wuwenfengmi1998/Morse_code_trainer/f103c8t6_keil/MDK-ARM/MYDEIVERS/oled.c

/*
 * oled.c
 *
 *  Created on: 2022年4月15日
 *      Author: wuwen
 */


#include "oled.h"

/*
通过IIC发送指令到OLED
*/
void OLED_WrCmd(unsigned char IIC_Command)
{
	uint8_t *pData;
	pData = &IIC_Command;
	IIC_SAND_DATE(OLED_ADDRESS,0x00,pData,1);
}
/*
通过IIC发送数据到OLED
*/
void OLED_WrDat(unsigned char IIC_Data)
{
	uint8_t *pData;
	pData = &IIC_Data;
	IIC_SAND_DATE(OLED_ADDRESS,0x40,pData,1);
}
/*
设置硬件内的光标
*/
void OLED_Set_Pos(unsigned char x, unsigned char y)
{
  OLED_WrCmd(    0xb0  +   7-y   );
  OLED_WrCmd(((x&0xf0)>>4)|0x10);
  OLED_WrCmd( (x&0x0f)    |0x00);
}
/*
初始化硬件内存（显存）
*/
void OLED_Init_Display_Buffer(char a)
{

	for(unsigned char y = 0;y < Y_WIDTH_;y++)
	{
		OLED_Set_Pos(0,y);
		for(unsigned char x = 0;x < X_WIDTH;x++)
		{

			OLED_WrDat(a);
			//HAL_Delay(1);
		}
	}


}
/*
设置屏幕亮度
*/
void OLED_Setting_luminance(unsigned char a)
{
	OLED_WrCmd(0x81);
	OLED_WrCmd(a*2.55);

}
/*
初始化OLED

硬件扫描方式

从左到右从上到下
纵向8点上高位

*/
void OLED_Init(void)
{
	//HAL_Delay(200);
	OLED_WrCmd(0xAE); //关闭显示
	OLED_WrCmd(0xD5); //设置时钟分频因子,震荡频率
	OLED_WrCmd(  80); //[3:0],分频因子;[7:4],震荡频率
	OLED_WrCmd(0xA8); //设置驱动路数
	OLED_WrCmd(0X3F); //默认0X3F(1/64)
	OLED_WrCmd(0xD3); //设置显示偏移
	OLED_WrCmd(0X00); //默认为0
	OLED_WrCmd(0x40); //设置显示开始行 [5:0],行数.
	OLED_WrCmd(0x8D); //电荷泵设置
	OLED_WrCmd(0x14); //bit2，开启/关闭
	OLED_WrCmd(0x20); //设置内存地址模式
	OLED_WrCmd(0x02); //[1:0],00，列地址模式;01，行地址模式;10,页地址模式;默认10;
	OLED_WrCmd(0xA1); //段重定义设置,bit0:0,0->0;1,0->127;
	OLED_WrCmd(0xC0); //设置COM扫描方向;bit3:0,普通模式;1,重定义模式 COM[N-1]->COM0;N:驱动路数
	//OLED_WrCmd(0xDA); //设置COM硬件引脚配置
	//OLED_WrCmd(0x12); //[5:4]配置
	//显示方向设置
	//OLED_WrCmd(0xc8);//OLED_WrCmd(0xa0);
	 //行扫描顺序：从上到下
	 //列扫描顺序：从左到右
	OLED_WrCmd(0xD9); //设置预充电周期
	OLED_WrCmd(0xf1); //[3:0],PHASE 1;[7:4],PHASE 2;
	OLED_WrCmd(0xDB); //设置VCOMH 电压倍率
	OLED_WrCmd(0x30); //[6:4] 000,0.65*vcc;001,0.77*vcc;011,0.83*vcc;

	OLED_WrCmd(0xA4); //全局显示开启;bit0:1,开启;0,关闭;(白屏/黑屏)
	OLED_WrCmd(0xA6);
	 //设置显示方式;bit0:1,反相显示;0,正常显示
	OLED_WrCmd(0xAF); //开启显示
	
	OLED_Init_Display_Buffer(0);
}

/*************************************************************************************************************************************************************************************/
/*硬件与软件之间的部分*/


/*
定义显存
*/
char OLED_buff[Y_WIDTH_][X_WIDTH];

/*
加速缓存
*/
char OLED_speedup[Y_WIDTH_][X_WIDTH];
/*
将显存发送到硬件
*/
void OLED_Cache_to_hardware()
{
	char b=0;
	for(uint8_t y=0;y<Y_WIDTH_;y++)
	{
		OLED_Set_Pos(0,y);
		for(uint8_t x=0;x<X_WIDTH;x++)
		{
			if(OLED_buff[y][x]!=OLED_speedup[y][x])
			{
				
				if(b==0){b=1;OLED_Set_Pos(x,y);}			
				OLED_WrDat(OLED_buff[y][x]);			
				OLED_speedup[y][x]=OLED_buff[y][x];
				
			}else
			{b=0;}
			OLED_buff[y][x]=0x00;
		}
	}
}


/*************************************************************************************************************************************************************************************/
//5*8 ASCII字符集点阵
const char asc2_0805[95][8]={
/*-- ID:0,字符:" ",ASCII编码:20,对应字:宽x高=5x8,画布:宽W=8 高H=8,共8字节*/
0x00,0x00,0x00,0x00,0x00,0x00,0x00,0x00,
/*-- ID:1,字符:"!",ASCII编码:21,对应字:宽x高=5x8,画布:宽W=8 高H=8,共8字节*/
0x20,0x20,0x20,0x20,0x20,0x00,0x20,0x00,
/*-- ID:2,字符:""",ASCII编码:22,对应字:宽x高=5x8,画布:宽W=8 高H=8,共8字节*/
0x50,0x50,0x50,0x00,0x00,0x00,0x00,0x00,
/*-- ID:3,字符:"#",ASCII编码:23,对应字:宽x高=5x8,画布:宽W=8 高H=8,共8字节*/
0x50,0x50,0xF8,0x50,0xF8,0x50,0x50,0x00,
/*-- ID:4,字符:"$",ASCII编码:24,对应字:宽x高=5x8,画布:宽W=8 高H=8,共8字节*/
0x20,0x78,0xC0,0x70,0x28,0xF0,0x20,0x00,
/*-- ID:5,字符:"%",ASCII编码:25,对应字:宽x高=5x8,画布:宽W=8 高H=8,共8字节*/
0xC0,0xC8,0x10,0x20,0x40,0x98,0x18,0x00,
/*-- ID:6,字符:"&",ASCII编码:26,对应字:宽x高=5x8,画布:宽W=8 高H=8,共8字节*/
0x40,0xA0,0xA0,0x40,0xA8,0x90,0x68,0x00,
/*-- ID:7,字符:"'",ASCII编码:27,对应字:宽x高=5x8,画布:宽W=8 高H=8,共8字节*/
0x30,0x20,0x40,0x00,0x00,0x00,0x00,0x00,
/*-- ID:8,字符:"(",ASCII编码:28,对应字:宽x高=5x8,画布:宽W=8 高H=8,共8字节*/
0x10,0x20,0x40,0x40,0x40,0x20,0x10,0x00,
/*-- ID:9,字符:")",ASCII编码:29,对应字:宽x高=5x8,画布:宽W=8 高H=8,共8字节*/
0x40,0x20,0x10,0x10,0x10,0x20,0x40,0x00,
/*-- ID:10,字符:"*",ASCII编码:2A,对应字:宽x高=5x8,画布:宽W=8 高H=8,共8字节*/
0x20,0xA8,0x70,0x20,0x70,0xA8,0x20,0x00,
/*-- ID:11,字符:"+",ASCII编码:2B,对应字:宽x高=5x8,画布:宽W=8 高H=8,共8字节*/
0x20,0x20,0x20,0xF8,0x20,0x20,0x20,0x00,
/*-- ID:12,字符:",",ASCII编码:2C,对应字:宽x高=5x8,画布:宽W=8 高H=8,共8字节*/
0x00,0x00,0x00,0x00,0x60,0x40,0x80,0x00,
/*-- ID:13,字符:"-",ASCII编码:2D,对应字:宽x高=5x8,画布:宽W=8 高H=8,共8字节*/
0x00,0x00,0x00,0xF8,0x00,0x00,0x00,0x00,
/*-- ID:14,字符:".",ASCII编码:2E,对应字:宽x高=5x8,画布:宽W=8 高H=8,共8字节*/
0x00,0x00,0x00,0x00,0x00,0x60,0x60,0x00,
/*-- ID:15,字符:"/",ASCII编码:2F,对应字:宽x高=5x8,画布:宽W=8 高H=8,共8字节*/
0x00,0x08,0x10,0x20,0x40,0x80,0x00,0x00,
/*-- ID:16,字符:"0",ASCII编码:30,对应字:宽x高=5x8,画布:宽W=8 高H=8,共8字节*/
0x70,0x88,0x98,0xA8,0xC8,0x88,0x70,0x00,
/*-- ID:17,字符:"1",ASCII编码:31,对应字:宽x高=5x8,画布:宽W=8 高H=8,共8字节*/
0x20,0x60,0x20,0x20,0x20,0x20,0x70,0x00,
/*-- ID:18,字符:"2",ASCII编码:32,对应字:宽x高=5x8,画布:宽W=8 高H=8,共8字节*/
0x70,0x88,0x08,0x30,0x40,0x80,0xF8,0x00,
/*-- ID:19,字符:"3",ASCII编码:33,对应字:宽x高=5x8,画布:宽W=8 高H=8,共8字节*/
0xF8,0x08,0x10,0x30,0x08,0x88,0x70,0x00,
/*-- ID:20,字符:"4",ASCII编码:34,对应字:宽x高=5x8,画布:宽W=8 高H=8,共8字节*/
0x10,0x30,0x50,0x90,0xF8,0x10,0x10,0x00,
/*-- ID:21,字符:"5",ASCII编码:35,对应字:宽x高=5x8,画布:宽W=8 高H=8,共8字节*/
0xF8,0x80,0xF0,0x08,0x08,0x88,0x70,0x00,
/*-- ID:22,字符:"6",ASCII编码:36,对应字:宽x高=5x8,画布:宽W=8 高H=8,共8字节*/
0x38,0x40,0x80,0xF0,0x88,0x88,0x70,0x00,
/*-- ID:23,字符:"7",ASCII编码:37,对应字:宽x高=5x8,画布:宽W=8 高H=8,共8字节*/
0xF8,0x08,0x10,0x20,0x40,0x40,0x40,0x00,
/*-- ID:24,字符:"8",ASCII编码:38,对应字:宽x高=5x8,画布:宽W=8 高H=8,共8字节*/
0x70,0x88,0x88,0x70,0x88,0x88,0x70,0x00,
/*-- ID:25,字符:"9",ASCII编码:39,对应字:宽x高=5x8,画布:宽W=8 高H=8,共8字节*/
0x70,0x88,0x88,0x78,0x08,0x10,0xE0,0x00,
/*-- ID:26,字符:":",ASCII编码:3A,对应字:宽x高=5x8,画布:宽W=8 高H=8,共8字节*/
0x00,0x60,0x60,0x00,0x60,0x60,0x00,0x00,
/*-- ID:27,字符:";",ASCII编码:3B,对应字:宽x高=5x8,画布:宽W=8 高H=8,共8字节*/
0x00,0x60,0x60,0x00,0x60,0x60,0x80,0x00,
/*-- ID:28,字符:"<",ASCII编码:3C,对应字:宽x高=5x8,画布:宽W=8 高H=8,共8字节*/
0x10,0x20,0x40,0x80,0x40,0x20,0x10,0x00,
/*-- ID:29,字符:"=",ASCII编码:3D,对应字:宽x高=5x8,画布:宽W=8 高H=8,共8字节*/
0x00,0x00,0xF8,0x00,0xF8,0x00,0x00,0x00,
/*-- ID:30,字符:">",ASCII编码:3E,对应字:宽x高=5x8,画布:宽W=8 高H=8,共8字节*/
0x40,0x20,0x10,0x08,0x10,0x20,0x40,0x00,
/*-- ID:31,字符:"?",ASCII编码:3F,对应字:宽x高=5x8,画布:宽W=8 高H=8,共8字节*/
0x70,0x88,0x10,0x20,0x20,0x00,0x20,0x00,
/*-- ID:32,字符:"@",ASCII编码:40,对应字:宽x高=5x8,画布:宽W=8 高H=8,共8字节*/
0x70,0x88,0xB8,0xA8,0xB8,0x80,0x78,0x00,
/*-- ID:33,字符:"A",ASCII编码:41,对应字:宽x高=5x8,画布:宽W=8 高H=8,共8字节*/
0x20,0x50,0x88,0x88,0xF8,0x88,0x88,0x00,
/*-- ID:34,字符:"B",ASCII编码:42,对应字:宽x高=5x8,画布:宽W=8 高H=8,共8字节*/
0xF0,0x88,0x88,0xF0,0x88,0x88,0xF0,0x00,
/*-- ID:35,字符:"C",ASCII编码:43,对应字:宽x高=5x8,画布:宽W=8 高H=8,共8字节*/
0x70,0x88,0x80,0x80,0x80,0x88,0x70,0x00,
/*-- ID:36,字符:"D",ASCII编码:44,对应字:宽x高=5x8,画布:宽W=8 高H=8,共8字节*/
0xF0,0x88,0x88,0x88,0x88,0x88,0xF0,0x00,
/*-- ID:37,字符:"E",ASCII编码:45,对应字:宽x高=5x8,画布:宽W=8 高H=8,共8字节*/
0xF8,0x80,0x80,0xF0,0x80,0x80,0xF8,0x00,
/*-- ID:38,字符:"F",ASCII编码:46,对应字:宽x高=5x8,画布:宽W=8 高H=8,共8字节*/
0xF8,0x80,0x80,0xF0,0x80,0x80,0x80,0x00,
/*-- ID:39,字符:"G",ASCII编码:47,对应字:宽x高=5x8,画布:宽W=8 高H=8,共8字节*/
0x70,0x88,0x80,0x80,0xB8,0x88,0x78,0x00,
/*-- ID:40,字符:"H",ASCII编码:48,对应字:宽x高=5x8,画布:宽W=8 高H=8,共8字节*/
0x88,0x88,0x88,0xF8,0x88,0x88,0x88,0x00,
/*-- ID:41,字符:"I",ASCII编码:49,对应字:宽x高=5x8,画布:宽W=8 高H=8,共8字节*/
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

/*-- ID:91,字符:"{",ASCII编码:7B,对应字:宽x高=8x16,画布:宽W=8 高H=16,共16字节*/
0x00,0x00,0x00,0x0E,0x18,0x18,0x18,0x70,0x18,0x18,0x18,0x18,0x0E,0x00,0x00,0x00,

/*-- ID:92,字符:"|",ASCII编码:7C,对应字:宽x高=8x16,画布:宽W=8 高H=16,共16字节*/
0x00,0x00,0x00,0x18,0x18,0x18,0x18,0x00,0x18,0x18,0x18,0x18,0x18,0x00,0x00,0x00,

/*-- ID:93,字符:"}",ASCII编码:7D,对应字:宽x高=8x16,画布:宽W=8 高H=16,共16字节*/
0x00,0x00,0x00,0x70,0x18,0x18,0x18,0x0E,0x18,0x18,0x18,0x18,0x70,0x00,0x00,0x00,

/*-- ID:94,字符:"~",ASCII编码:7E,对应字:宽x高=8x16,画布:宽W=8 高H=16,共16字节*/
0x00,0x00,0x00,0x76,0xDC,0x00,0x00,0x00,0x00,0x00,0x00,0x00,0x00,0x00,0x00,0x00

};

/*
打点函数
打点类型
dot_type=0 清除点
				=1 打点
				=2 取反点
*/
void OLED_set_dot(unsigned char x,unsigned char y,unsigned char dot_type)
{
	if(x>=X_WIDTH||y>=Y_WIDTH)
	{
		return ;
	}
	uint8_t y1=y/8;
	uint8_t y2=y%8;
	uint8_t y3=(0x80>>y2);
	
	char temp=OLED_buff[y1][x];
	switch(dot_type)
	{
		case 0:
			temp &= ~y3;
			break;
		case 1:
			temp |= y3;
			break;
		case 2:
			temp ^= y3;
			break;
		case 3:break;
	}
	
	
	OLED_buff[y1][x]=temp;
		
		
	
	
}
/*
绘图函数
数据格式 从左到右，从上到下，横向8点右高位
type=0 清空区域
		=1 区域图层
		=2 正片叠底
		=3 正片清空
		=4 负片
		=5 正片负片
*/
void OLED_Pix(unsigned char x,unsigned char y,unsigned char w,unsigned char h,const char *p,unsigned char type)
{
	
	unsigned char b=0;
	unsigned int  c=0;
	
	for(uint8_t h1=0;h1<h;h1++)
	{
		for(uint8_t w1=0;w1<w;w1++)
		{
			if(p[c]&0x80>>b)
			{
				switch(type)
				{
					case 0:
						OLED_set_dot(w1+x,h1+y,0);
						break;
					case 1:
						OLED_set_dot(w1+x,h1+y,1);
						break;
					case 2:
						OLED_set_dot(w1+x,h1+y,1);
						break;		
					case 3:
						OLED_set_dot(w1+x,h1+y,0);
						break;		
					case 4:
						OLED_set_dot(w1+x,h1+y,0);
						break;	
					case 5:
						OLED_set_dot(w1+x,h1+y,2);
						break;						
				}
				
			}else
			{
				switch(type)
				{
					case 0:
						OLED_set_dot(w1+x,h1+y,0);
						break;
					case 1:
						OLED_set_dot(w1+x,h1+y,0);
						break;
					case 2:

						break;	
					case 4:
						OLED_set_dot(w1+x,h1+y,1);
						break;
				}
			}
			b++;
			if(b==8)
			{
				b=0;c++;
			}
		}
		if(b!=0)
		{
			b=0;c++;
		}
		
	}
		
	

}
/*
显示字符
数据格式 从左到右，从上到下，横向8点左高位 （同一个函数实现的显示不知道为何这里要用左高位才能正常显示）
type=0 清空区域
		=1 区域图层
		=2 正片叠底
		=3 正片清空
		=4 负片
*/
void OLED_Ascii(unsigned char x,unsigned char y,unsigned char size,char chr,unsigned char type)
{
	if(chr>=' '&&chr<='~')
	{
		switch(size)
		{
			case 8:
				OLED_Pix(x,y,5,8,asc2_0805[chr-' '],type);
				break;			
			case 12:
				OLED_Pix(x,y,6,12,asc2_1206[chr-' '],type);
				break;
			case 16:
				OLED_Pix(x,y,8,16,asc2_1608[chr-' '],type);
				break;
		}	
	}

}

void OLED_Str(unsigned char x,unsigned char y,unsigned char size,char *str,unsigned char type)
{
	unsigned char size2;
	switch(size)
	{
		case 8:
			size2=6;
		break;
		case 12:
			size2=7;
		break;
		case 16:
			size2=8;
		break;
	}	
	
	while(*str!='\0')
	{
		if(x+size2>=X_WIDTH)
		{
			y+=size;
			if(y>=Y_WIDTH)
			{
				y=0;
			}
			x=0;
		}

		OLED_Ascii(x,y,size,*str,type);

		str++;
		
		x+=size2;
		
		

	}

}

/*
几何绘图
*/


/*画横线*/
void OLED_HL(unsigned char x,unsigned char y,unsigned char size,unsigned char dot_type)
{

}

/*画竖线*/
void OLED_VL(unsigned char x,unsigned char y,unsigned char size,unsigned char dot_type)
{

}

/*画任意线*/
void OLED_AL(int sx,int sy,int ex,int ey,unsigned char dot_type)
{

	int dx,dy,absx,absy;
	
	//计算差
	dx=ex-sx;
	dy=ey-sy;
	//取绝对值 就是轴长
	absx=dx<0?0-dx:dx;
	absy=dy<0?0-dy:dy;
	
	
	if(dx==0)
	{
		if(dy>0)
		{
			for(int y=ey;y>sy;y--)
			{
				OLED_set_dot(sx,y,dot_type);
			}
		}else 
		if(dy<0)
		{
			for(int y=ey;y<sy;y++)
			{
				OLED_set_dot(sx,y,dot_type);
			}
		}
		
		return ;
	}

	if(dy==0)
	{
		if(dx>0)
		{
			for(int x=ex;x>sx;x--)
			{
				OLED_set_dot(x,sy,dot_type);
			}
		}else
		if(dx<0)
		{
			for(int x=ex;x<sx;x++)
			{
				OLED_set_dot(x,sy,dot_type);
			}
		}
		
		return ;
	}
	
	if(dx==0&&dy==0)
	{
		//OLED_set_dot(sx,sy,dot_type);
		return ;
	}
}


/*画方框*/
void OLED_square(int Start_x, int Start_y, int End_x, int End_y, char type)
{
	if(Start_x > End_x){int i1 = Start_x; Start_x = End_x; End_x=i1;}
	if(Start_y > End_y){int i1 = Start_y; Start_y = End_y; End_y=i1;}
	for(; Start_x < End_x ; Start_x++)
	{
		for(int y2 = Start_y ; y2 < End_y ; y2++)
		{
			OLED_set_dot(Start_x, y2, type);
		}
	}
}

int SHOW_MENU(menu *m,int encoder,char button,char lan)
{
	int return_code=-1;
	char str[32];
	const char *list;
	uint16_t list_len=0;
	uint16_t a=0;
	uint16_t b=0;
	uint16_t c=0;
	uint16_t d=0;

	//get list
	switch(lan)
	{
	case 0:
		list=m->list_en;
		break;
	case 1:
		list=m->list_ch;
		break;
	default :
		return -1;

	}



	//check how many list
	while(list[a]!='\0')
	{
		if(list[a]=='\n'){list_len++;}
		a++;
	}

	m->sele+=encoder;

	if(m->sele<0){m->sele=0;}
	if(m->sele>list_len){m->sele=list_len;}

	if(m->sele<m->list_dis_top+3){m->list_dis_top--;}
	if(m->sele>m->list_dis_top){if((m->list_dis_top+3)<list_len){m->list_dis_top++;}}

	m->list_dis_top=((list_len+1>4)?(m->list_dis_top):0);

	//display list
	for(d=0;d<m->list_dis_top;d++)
	{
		while((*list!='\0')&&(*list!='\n'))
		{
			list++;
		}
		list++;

	}


	for(b=0;b<(list_len+1>4?4:list_len+1);b++)
	{
		if((m->list_dis_top+b)==m->sele)
		{
			str[c]='>';

		}else
		{
			str[c]=' ';
		}
		c++;
		while((*list!='\0')&&(*list!='\n'))
		{
			str[c]=*list;
			c++;
			list++;
		}
		str[c]='\0';
		OLED_Str(0, 16*b, 16, str, 1);
		c=0;
		list++;

	}

	if(button==1)
	{
		return_code=m->sele;
	}

	return return_code;

}
