wuwenfengmi1998/Morse_code_trainer/f103c8t6_HAL/MYDRIVERS/oled.c

/*
 * oled.c
 *
 *  Created on: 2022年4月15日
 *      Author: wuwen
 */


#include "oled.h"


//16*16 ASCII字符集点阵
const unsigned char asc2_1608[95][16]={
{0x00,0x00,0x00,0x00,0x00,0x00,0x00,0x00,0x00,0x00,0x00,0x00,0x00,0x00,0x00,0x00},/*" ",0*/
{0x00,0x00,0x00,0x00,0x00,0x00,0x1F,0xCC,0x00,0x0C,0x00,0x00,0x00,0x00,0x00,0x00},/*"!",1*/
{0x00,0x00,0x08,0x00,0x30,0x00,0x60,0x00,0x08,0x00,0x30,0x00,0x60,0x00,0x00,0x00},/*""",2*/
{0x02,0x20,0x03,0xFC,0x1E,0x20,0x02,0x20,0x03,0xFC,0x1E,0x20,0x02,0x20,0x00,0x00},/*"#",3*/
{0x00,0x00,0x0E,0x18,0x11,0x04,0x3F,0xFF,0x10,0x84,0x0C,0x78,0x00,0x00,0x00,0x00},/*"$",4*/
{0x0F,0x00,0x10,0x84,0x0F,0x38,0x00,0xC0,0x07,0x78,0x18,0x84,0x00,0x78,0x00,0x00},/*"%",5*/
{0x00,0x78,0x0F,0x84,0x10,0xC4,0x11,0x24,0x0E,0x98,0x00,0xE4,0x00,0x84,0x00,0x08},/*"&",6*/
{0x08,0x00,0x68,0x00,0x70,0x00,0x00,0x00,0x00,0x00,0x00,0x00,0x00,0x00,0x00,0x00},/*"'",7*/
{0x00,0x00,0x00,0x00,0x00,0x00,0x07,0xE0,0x18,0x18,0x20,0x04,0x40,0x02,0x00,0x00},/*"(",8*/
{0x00,0x00,0x40,0x02,0x20,0x04,0x18,0x18,0x07,0xE0,0x00,0x00,0x00,0x00,0x00,0x00},/*")",9*/
{0x02,0x40,0x02,0x40,0x01,0x80,0x0F,0xF0,0x01,0x80,0x02,0x40,0x02,0x40,0x00,0x00},/*"*",10*/
{0x00,0x80,0x00,0x80,0x00,0x80,0x0F,0xF8,0x00,0x80,0x00,0x80,0x00,0x80,0x00,0x00},/*"+",11*/
{0x00,0x01,0x00,0x0D,0x00,0x0E,0x00,0x00,0x00,0x00,0x00,0x00,0x00,0x00,0x00,0x00},/*",",12*/
{0x00,0x00,0x00,0x80,0x00,0x80,0x00,0x80,0x00,0x80,0x00,0x80,0x00,0x80,0x00,0x80},/*"-",13*/
{0x00,0x00,0x00,0x0C,0x00,0x0C,0x00,0x00,0x00,0x00,0x00,0x00,0x00,0x00,0x00,0x00},/*".",14*/
{0x00,0x00,0x00,0x06,0x00,0x18,0x00,0x60,0x01,0x80,0x06,0x00,0x18,0x00,0x20,0x00},/*"/",15*/
{0x00,0x00,0x07,0xF0,0x08,0x08,0x10,0x04,0x10,0x04,0x08,0x08,0x07,0xF0,0x00,0x00},/*"0",16*/
{0x00,0x00,0x08,0x04,0x08,0x04,0x1F,0xFC,0x00,0x04,0x00,0x04,0x00,0x00,0x00,0x00},/*"1",17*/
{0x00,0x00,0x0E,0x0C,0x10,0x14,0x10,0x24,0x10,0x44,0x11,0x84,0x0E,0x0C,0x00,0x00},/*"2",18*/
{0x00,0x00,0x0C,0x18,0x10,0x04,0x11,0x04,0x11,0x04,0x12,0x88,0x0C,0x70,0x00,0x00},/*"3",19*/
{0x00,0x00,0x00,0xE0,0x03,0x20,0x04,0x24,0x08,0x24,0x1F,0xFC,0x00,0x24,0x00,0x00},/*"4",20*/
{0x00,0x00,0x1F,0x98,0x10,0x84,0x11,0x04,0x11,0x04,0x10,0x88,0x10,0x70,0x00,0x00},/*"5",21*/
{0x00,0x00,0x07,0xF0,0x08,0x88,0x11,0x04,0x11,0x04,0x18,0x88,0x00,0x70,0x00,0x00},/*"6",22*/
{0x00,0x00,0x1C,0x00,0x10,0x00,0x10,0xFC,0x13,0x00,0x1C,0x00,0x10,0x00,0x00,0x00},/*"7",23*/
{0x00,0x00,0x0E,0x38,0x11,0x44,0x10,0x84,0x10,0x84,0x11,0x44,0x0E,0x38,0x00,0x00},/*"8",24*/
{0x00,0x00,0x07,0x00,0x08,0x8C,0x10,0x44,0x10,0x44,0x08,0x88,0x07,0xF0,0x00,0x00},/*"9",25*/
{0x00,0x00,0x00,0x00,0x00,0x00,0x03,0x0C,0x03,0x0C,0x00,0x00,0x00,0x00,0x00,0x00},/*":",26*/
{0x00,0x00,0x00,0x00,0x00,0x01,0x01,0x06,0x00,0x00,0x00,0x00,0x00,0x00,0x00,0x00},/*";",27*/
{0x00,0x00,0x00,0x80,0x01,0x40,0x02,0x20,0x04,0x10,0x08,0x08,0x10,0x04,0x00,0x00},/*"<",28*/
{0x02,0x20,0x02,0x20,0x02,0x20,0x02,0x20,0x02,0x20,0x02,0x20,0x02,0x20,0x00,0x00},/*"=",29*/
{0x00,0x00,0x10,0x04,0x08,0x08,0x04,0x10,0x02,0x20,0x01,0x40,0x00,0x80,0x00,0x00},/*">",30*/
{0x00,0x00,0x0E,0x00,0x12,0x00,0x10,0x0C,0x10,0x6C,0x10,0x80,0x0F,0x00,0x00,0x00},/*"?",31*/
{0x03,0xE0,0x0C,0x18,0x13,0xE4,0x14,0x24,0x17,0xC4,0x08,0x28,0x07,0xD0,0x00,0x00},/*"@",32*/
{0x00,0x04,0x00,0x3C,0x03,0xC4,0x1C,0x40,0x07,0x40,0x00,0xE4,0x00,0x1C,0x00,0x04},/*"A",33*/
{0x10,0x04,0x1F,0xFC,0x11,0x04,0x11,0x04,0x11,0x04,0x0E,0x88,0x00,0x70,0x00,0x00},/*"B",34*/
{0x03,0xE0,0x0C,0x18,0x10,0x04,0x10,0x04,0x10,0x04,0x10,0x08,0x1C,0x10,0x00,0x00},/*"C",35*/
{0x10,0x04,0x1F,0xFC,0x10,0x04,0x10,0x04,0x10,0x04,0x08,0x08,0x07,0xF0,0x00,0x00},/*"D",36*/
{0x10,0x04,0x1F,0xFC,0x11,0x04,0x11,0x04,0x17,0xC4,0x10,0x04,0x08,0x18,0x00,0x00},/*"E",37*/
{0x10,0x04,0x1F,0xFC,0x11,0x04,0x11,0x00,0x17,0xC0,0x10,0x00,0x08,0x00,0x00,0x00},/*"F",38*/
{0x03,0xE0,0x0C,0x18,0x10,0x04,0x10,0x04,0x10,0x44,0x1C,0x78,0x00,0x40,0x00,0x00},/*"G",39*/
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
};



void OLED_WrCmd(unsigned char IIC_Command)
{
	uint8_t *pData;
	pData = &IIC_Command;
	IIC_SAND_DATE(OLED_ADDRESS,0x00,pData,1);
}

void OLED_WrDat(unsigned char IIC_Data)
{
	uint8_t *pData;
	pData = &IIC_Data;
	IIC_SAND_DATE(OLED_ADDRESS,0x40,pData,1);
}

void OLED_Set_Pos(unsigned char x, unsigned char y)
{
  OLED_WrCmd(    0xb0  +   7-y   );
  OLED_WrCmd(((x&0xf0)>>4)|0x10);
  OLED_WrCmd( (x&0x0f)    |0x00);
}

void OLED_Init_Display_Buffer(char a)
{

	for(unsigned char y = 0;y < Y_WIDTH_;y++)
	{
		OLED_Set_Pos(0,y);
		for(unsigned char x = 0;x < X_WIDTH;x++)
		{

			OLED_WrDat(a);
			//HAL_Delay(1);
		}
	}


}

void OLED_Setting_luminance(unsigned char a)
{
	OLED_WrCmd(0x81);
	OLED_WrCmd(a*2.55);

}

void OLED_Init(void)
{
	//HAL_Delay(200);
	OLED_WrCmd(0xAE); //关闭显示
	OLED_WrCmd(0xD5); //设置时钟分频因子,震荡频率
	OLED_WrCmd(  80); //[3:0],分频因子;[7:4],震荡频率
	OLED_WrCmd(0xA8); //设置驱动路数
	OLED_WrCmd(0X3F); //默认0X3F(1/64)
	OLED_WrCmd(0xD3); //设置显示偏移
	OLED_WrCmd(0X00); //默认为0
	OLED_WrCmd(0x40); //设置显示开始行 [5:0],行数.
	OLED_WrCmd(0x8D); //电荷泵设置
	OLED_WrCmd(0x14); //bit2，开启/关闭
	OLED_WrCmd(0x20); //设置内存地址模式
	OLED_WrCmd(0x02); //[1:0],00，列地址模式;01，行地址模式;10,页地址模式;默认10;
	OLED_WrCmd(0xA1); //段重定义设置,bit0:0,0->0;1,0->127;
	OLED_WrCmd(0xC0); //设置COM扫描方向;bit3:0,普通模式;1,重定义模式 COM[N-1]->COM0;N:驱动路数
	//OLED_WrCmd(0xDA); //设置COM硬件引脚配置
	//OLED_WrCmd(0x12); //[5:4]配置
	//显示方向设置
	//OLED_WrCmd(0xc8);//OLED_WrCmd(0xa0);
	 //行扫描顺序：从上到下
	 //列扫描顺序：从左到右
	OLED_WrCmd(0xD9); //设置预充电周期
	OLED_WrCmd(0xf1); //[3:0],PHASE 1;[7:4],PHASE 2;
	OLED_WrCmd(0xDB); //设置VCOMH 电压倍率
	OLED_WrCmd(0x30); //[6:4] 000,0.65*vcc;001,0.77*vcc;011,0.83*vcc;

	OLED_WrCmd(0xA4); //全局显示开启;bit0:1,开启;0,关闭;(白屏/黑屏)
	OLED_WrCmd(0xA6);
	 //设置显示方式;bit0:1,反相显示;0,正常显示
	OLED_WrCmd(0xAF); //开启显示
}



void OLED_ShowChar(unsigned char x,unsigned char y,unsigned char chr)
{
	OLED_Set_Pos(x,y);
	for(char a=0;a<8;a++)
	{
		OLED_WrDat(asc2_1608[chr-' '][(a*2)]);
	}
	OLED_Set_Pos(x,y+1);
	for(char a=0;a<8;a++)
	{
		OLED_WrDat(asc2_1608[chr-' '][(a*2)+1]);
	}
}

void OLED_ShowStr(unsigned char x,unsigned char y,char *str)
{
	while(*str!='\0')
	{
		if(x>=X_WIDTH)
		{
			y+=2;
			if(y>=Y_WIDTH_)
			{
				y=0;
			}
			x=0;
		}

		OLED_ShowChar(x,y,*str);

		str++;
		x+=8;

	}

}
