wuwenfengmi1998/Morse_code_trainer/f103c8t6_keil/MDK-ARM/MYDEIVERS/mymain.h

/*
 * mymain.h
 *
 *  Created on: 2022年4月15日
 *      Author: wuwen
 */

#ifndef MYMAIN_H_
#define MYMAIN_H_

#include "main.h"
#include "oled.h"
#include "buzzer.h"
#include "encode.h"
#include "hread_interface.h"
#include "morsr.h"


extern TIM_HandleTypeDef htim3;

void mymain();

#endif /* MYMAIN_H_ */
