wuwenfengmi1998/Morse_code_trainer/stm32F030F4_code/mydrivers/interface.c

/*
 * interface.c
 *
 *  Created on: 2022年3月27日
 *      Author: wuwen
 */

#include "interface.h"

extern I2C_HandleTypeDef hi2c1;

void IIC_SAND_DATE(uint16_t DEVICE_ADD,uint16_t IN_DEVICE_ADD,char *DATAS,uint16_t LONG)
{
	HAL_I2C_Mem_Write(&hi2c1,DEVICE_ADD,IN_DEVICE_ADD,I2C_MEMADD_SIZE_8BIT,DATAS,LONG,100);
}

void IIC_READ_DATE(uint16_t DEVICE_ADD,uint16_t IN_DEVICE_ADD,char *DATAS,uint16_t LONG)
{
	HAL_I2C_Mem_Read(&hi2c1,DEVICE_ADD,IN_DEVICE_ADD,I2C_MEMADD_SIZE_8BIT,DATAS,LONG,100);
}
